KRMananduwa/Smart_Energy_Meter/PCB Designed By  Eagle/SmartMeter.sch

## EAGLE design PCB Designed By Eagle/SmartMeter.sch

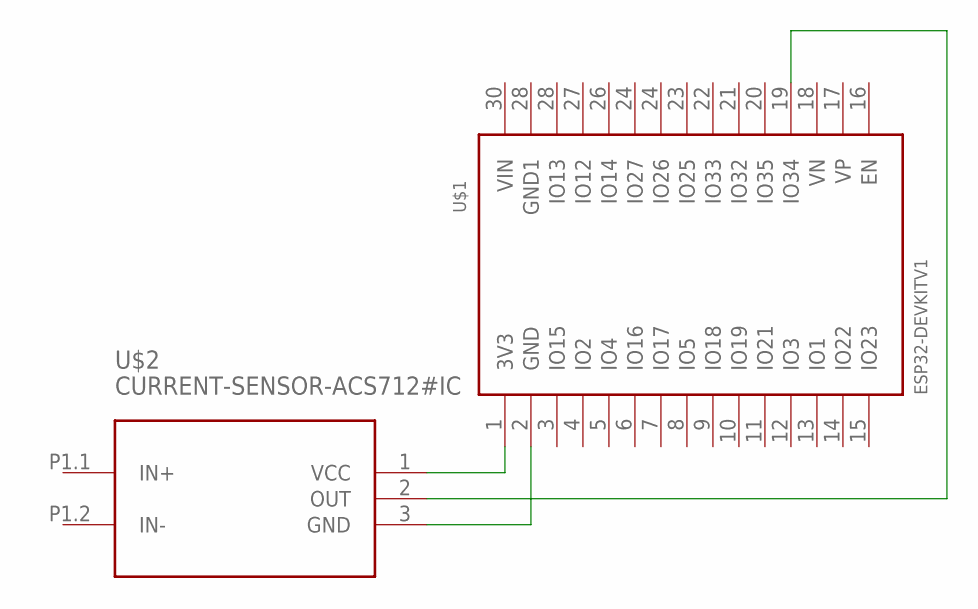
[picture p11: schematic SmartMeter.sch]

Parts:
U$1: ESP32DEVKITV1; ESP32-DEVKITV1
U$2: CURRENT-SENSOR-ACS712#IC

Connections:
unnamed: U$1.1 (3V3), U$2.1 (VCC)
unnamed: U$1.2 (GND), U$2.3 (GND)
unnamed: U$1.19 (IO34), U$2.2 (OUT)
