KRMananduwa/Smart_Energy_Meter/Software/Final Tested Programs/acs712digest/acs712digest.ino

#include "ACS712.h"
char watt[5];
ACS712 sensor(ACS712_30A, A1);
unsigned long last_time =0;
unsigned long current_time =0;
float Wh =0 ;  
void setup() {
  Serial.begin(115200);
  sensor.calibrate();
}

void loop() {
  float V = 230;
  float I = sensor.getCurrentAC();
// Serial.println(I);
  float P = V * I;
  last_time = current_time;
  current_time = millis();    
  Wh = Wh+  P *(( current_time -last_time) /3600000.0) ; 
   dtostrf(Wh, 4, 2, watt);        
Serial.println(watt);
  delay(10000);
}
