KRMananduwa/Smart_Energy_Meter/Software/Final Tested Programs/ardToEspCom/ard2espCom-EspCode/ard2espCom-EspCode.ino

void setup() {
  // Open serial communications and wait for port to open:
  Serial.begin(115200);
  while (!Serial) {
    ; // wait for serial port to connect. Needed for native USB port only
    }
}
void loop() { // run over and over
  if (Serial.available()) {
    Serial.write(Serial.read());
    }
}
